HelsinkiHacklab/partyhatwork/software/arduino/partyhatwork/rgb.h

#ifndef RGB_H
#define RGB_H
#include <Arduino.h>
#include "gammaramp.h"
#include "batterymonitor.h"

/**
 * Adjusts the PWM width based on battery voltage
 *
 * TODO: Implement some actual adjustment curve
 */
uint8_t pwmlimit(uint8_t pwm)
{
    // TODO: precalculate the limit factor (possibly in batterymonitor.h)
    int foo = batterymonitor.bat_mv;
    return pwm - (pwm >> 2);
}

/**
 * Generic setter for 3 consequtve PWM pins
 */
void setRGB(uint8_t startpin, uint8_t r, uint8_t g, uint8_t b)
{
    byte rgamma = gamma256to256(r);
    byte bgamma = gamma256to256(b);
    byte ggamma = gamma256to256(g);
    analogWrite(startpin, pwmlimit(rgamma));
    analogWrite(startpin+1, pwmlimit(ggamma));
    analogWrite(startpin+2, pwmlimit(bgamma));
}

/**
 * Set the first set of built-in drivers
 */
inline void setRGB0(uint8_t r, uint8_t g, uint8_t b)
{
    setRGB(16, r,g,b);
}

/**
 * Set the second set of built-in drivers
 */
inline void setRGB1(uint8_t r, uint8_t g, uint8_t b)
{
    setRGB(19, r,g,b);
}

inline void setStdRGB(uint8_t ledno, uint8_t r, uint8_t g, uint8_t b)
{
    switch(ledno)
    {
        case 0x0:
          setRGB0(r,g,b);
          break;
        case 0x1:
          setRGB1(r,g,b);
          break;
    }
}

// TODO: move the RGB interpolation code from the animationrunnner to here so it can be used elsewhere 


#endif
