HelsinkiHacklab/partyhatwork/software/arduino/partyhatwork/batterymonitor.h

#ifndef BATTERYMONITOR_H
#ifndef BAT_SENSE_PIN
#error "BAT_SENSE_PIN not defined"
#endif
#define BATTERYMONITOR_H
#include <Arduino.h>
#include <Task.h>

class BatteryMonitor : public TimedTask
{
public:
    // Create a new blinker for the specified pin and rate.
    BatteryMonitor(uint8_t _pin);
    virtual void run(uint32_t now);
    int bat_mv;
    int adc_value;
private:
    uint8_t pin;      // ADC pin
};

BatteryMonitor::BatteryMonitor(uint8_t _pin)
: TimedTask(millis()),
  pin(_pin)
{
    pinMode(pin, INPUT);     // Set pin for output.
}

void BatteryMonitor::run(uint32_t now)
{
    // Start by setting the next runtime
    incRunTime(15000);
    adc_value = analogRead(pin);
    // TODO: Map the value to mV
    // TODO: keep a running average for less noisy voltage
}

BatteryMonitor batterymonitor(BAT_SENSE_PIN);
extern BatteryMonitor batterymonitor;

void high_current_chg(boolean mode)
{
    if (mode)
    {
        pinMode(HIGH_CURRENT_CHG_PIN, OUTPUT);
        digitalWrite(HIGH_CURRENT_CHG_PIN, LOW);
    }
    else
    {
        pinMode(HIGH_CURRENT_CHG_PIN, INPUT);
    }
}



#endif
