HelsinkiHacklab/partyhatwork/software/arduino/animationtests/animations.h

#ifndef ANIMATION_H
#define ANIMATION_H
#include "animation_tasks.h"

#define FIRST_ANIMATION bar_anim 

const uint8_t foo_frames[] PROGMEM = { 
  0x0,  0x0, 0x0,    0x0, 0x0, 0x0,     0x1, 0xf4, // First frame, RGB values for two leds and unsigned interget wait time in ms
  0xff, 0x0, 0x0,    0x0, 0x0, 0x0,     0x1, 0xf4,
  0x0,  0x0, 0x0,    0x0, 0x0, 0xff,    0x1, 0xf4,
  0xff, 0x0, 0x0,    0x0, 0x0, 0x0,     0x1, 0xf4,
  0x0,  0x0, 0x0,    0x0, 0x0, 0xff,    0x1, 0xf4,
  0xff, 0x0, 0x0,    0x0, 0x0, 0xff,    0x5, 0xdc,
};

const Animation foo_anim PROGMEM = {
    0x0,
    0x3, // leds 0 & 1
    0x6,
    0x1,
    foo_frames  // Array name is always a pointer so no need for &
};

const uint8_t bar_frames[] PROGMEM = { 
  0x0,  0x0,  0x0,    0x0, 0x0,  0x0,    0x1, 0xf4, // First frame, RGB values for two leds and unsigned interget wait time in ms
  0x0,  0xff, 0x0,    0x0, 0x0,  0x0,    0x1, 0xf4,
  0x0,  0x0,  0x0,    0x0, 0xff, 0x0,    0x1, 0xf4,
  0x0,  0xff, 0x0,    0x0, 0x0,  0x0,    0x1, 0xf4,
  0x0,  0x0,  0x0,    0x0, 0xff, 0x0,    0x1, 0xf4,
  0x0,  0xff, 0x0,    0x0, 0xff, 0x0,    0x5, 0xdc,
};


const Animation bar_anim PROGMEM = {
    &foo_anim, // Pointer to the next animation in the chain
    0x3, // leds 0 & 1
    0x6,
    0x1,
    bar_frames // Array name is always a pointer so no need for &
};



#endif
